mandeeps/SU-WaterCam/tools/transmit_ip.py

"""IP uplink/downlink transport for SU-WaterCam.

Sends sensor channel data to the WaterCam FastAPI server over HTTP (WiFi or
cellular) and polls for queued downlink commands.  Designed to run outside of
TickTalkPython so the logic can be tested standalone before integration.

Usage (module)
--------------
    from tools.transmit_ip import IPTransmitter
    tx = IPTransmitter()                  # reads runtime_config.json
    result = tx.send_uplink(channels)     # {"success": bool, "status_code": int|None, ...}
    reply  = tx.poll_downlink()           # {"success": bool, "status_code": int|None, "command": dict|None, ...}
    cmd    = reply["command"]             # dict or None

Usage (CLI smoke-test)
----------------------
    python tools/transmit_ip.py

Configuration
-------------
All settings live in runtime_config.json under the "ip_upload" key.  See the
project docs/IP_TRANSMISSION.md for a full field reference.

Channel format
--------------
Each element of `channels` must match the ChannelItem schema the server expects:
    {"code": "02 01", "payload_hex": "00000064"}

Codes used by this device (from API CHANNEL_REGISTRY):
    "00 01"  device_ts        (8 bytes, UNIX seconds as u64 big-endian)
    "02 01"  battery_pct      (4 bytes, uint32)
    "03 01"  imu_block        (12 bytes)
    "04 01"  gps_block        (8 bytes: lat int32 /1e6, lon int32 /1e6)
    "05 01"  temperature_c    (2 bytes, int16 /100.0)
    "06 01"  humidity_pct     (1 byte, uint8)
    "07 17"  camera_flood_detect  (4 bytes, bool as uint32)
    "07 27"  camera_new_local_max (4 bytes, bool as uint32)
    "08 18"  camera_flood_bitmap  (variable length, raw bitmap bytes as hex string)
    "09 19"  sr_area_threshold_pct        (4 bytes)
    "09 29"  sr_stage_threshold_cm        (4 bytes)
    "09 39"  sr_monitoring_frequency      (4 bytes)
    "09 49"  sr_emergency_frequency       (4 bytes)
    "09 59"  sr_neighborhood_emerg_freq   (4 bytes)
"""

from __future__ import annotations

import json
import logging
import os
import subprocess
import time
from typing import Any, Callable, Dict, List, Optional

import requests

logger = logging.getLogger(__name__)

# Default config path — relative to the project root (one level above tools/).
_DEFAULT_CONFIG_PATH = os.path.join(
    os.path.dirname(__file__), "..", "runtime_config.json"
)

# Pending-uplink queue directory — persists failed readings for retry next cycle.
_DEFAULT_QUEUE_DIR = os.path.join(
    os.path.dirname(__file__), "..", "data", "ip_uplink_pending"
)


def _coerce_int(value: Any, default: int) -> int:
    """Return ``int(value)`` or ``default`` if value is missing/invalid."""
    try:
        return int(value)
    except (TypeError, ValueError):
        return default


def _coerce_float(value: Any, default: float) -> float:
    """Return ``float(value)`` or ``default`` if value is missing/invalid."""
    try:
        return float(value)
    except (TypeError, ValueError):
        return default


def _load_ip_config(config_path: str = _DEFAULT_CONFIG_PATH) -> Dict[str, Any]:
    """Load and return the ip_upload section from runtime_config.json.

    Returns an empty dict (all defaults) if the file is missing or contains
    invalid JSON — runtime_config.json is gitignored and may not exist in fresh
    dev or CI environments.
    """
    try:
        with open(config_path) as f:
            cfg = json.load(f)
    except OSError as exc:
        # Covers FileNotFoundError, PermissionError, and other I/O failures.
        logger.debug("Cannot read config at %s (%s); using defaults", config_path, exc)
        return {}
    except json.JSONDecodeError as exc:
        logger.warning("Invalid JSON in %s: %s; using defaults", config_path, exc)
        return {}
    if not isinstance(cfg, dict):
        logger.warning("Unexpected config format in %s; using defaults", config_path)
        return {}
    ip_cfg = cfg.get("ip_upload", {})
    if not isinstance(ip_cfg, dict):
        logger.warning("ip_upload in %s is not an object; using defaults", config_path)
        return {}
    return ip_cfg


class IPTransmitter:
    """Handles uplink posting and downlink polling over HTTP.

    Parameters
    ----------
    config_path:
        Path to runtime_config.json.  Defaults to the project-root copy.
    override_url:
        If provided, overrides the server_url from config (useful in tests).
    override_device_id:
        If provided, overrides the device_id from config.

    Notes
    -----
    ``self.enabled`` reflects the ``ip_upload.enabled`` config flag, but
    ``send_uplink()`` and ``poll_downlink()`` do **not** check it internally —
    the flag is an integration-layer concern enforced by ``ticktalk_main.py``.
    Direct callers (tests, CLI smoke-test) are responsible for checking
    ``tx.enabled`` themselves if they want to respect the flag.
    """

    def __init__(
        self,
        config_path: str = _DEFAULT_CONFIG_PATH,
        override_url: Optional[str] = None,
        override_device_id: Optional[str] = None,
        queue_dir: Optional[str] = None,
    ) -> None:
        cfg = _load_ip_config(config_path)

        self.enabled: bool = cfg.get("enabled", False)
        self.server_url: str = (override_url or cfg.get("server_url", "http://localhost:8000")).rstrip("/")
        self.api_key: str = cfg.get("api_key", "")
        self.device_id: str = override_device_id or cfg.get("device_id", "watercam-001")
        self.timeout_s: int = max(1, _coerce_int(cfg.get("timeout_s"), 15))
        self.retry_attempts: int = max(1, _coerce_int(cfg.get("retry_attempts"), 3))
        self.retry_backoff_s: float = _coerce_float(cfg.get("retry_backoff_s"), 2.0)
        self.fallback_to_lora: bool = cfg.get("fallback_to_lora", True)
        self.max_queue_depth: int = max(1, _coerce_int(cfg.get("max_queue_depth"), 48))
        self.max_queue_age_days: float = max(0.0, _coerce_float(cfg.get("max_queue_age_days"), 7.0))
        # Transport order LoRa -> WiFi -> cellular: skip the IP uplink while
        # the mDot is joined, and use the named NetworkManager connection only
        # when the server can't be reached without it.
        self.only_if_lora_unavailable: bool = cfg.get("only_if_lora_unavailable", True) is not False
        cell = cfg.get("cellular_connection", "Quectel")
        self.cellular_connection: str = cell if isinstance(cell, str) else ""
        self.cellular_connect_timeout_s: int = max(5, _coerce_int(cfg.get("cellular_connect_timeout_s"), 90))
        self._queue_dir: str = os.path.abspath(queue_dir or _DEFAULT_QUEUE_DIR)

        self._session = requests.Session()
        if self.api_key:
            self._session.headers.update({"Authorization": f"Bearer {self.api_key}"})
        self._session.headers.update({"Content-Type": "application/json"})

    # ------------------------------------------------------------------ #
    # Public API                                                           #
    # ------------------------------------------------------------------ #

    def send_uplink(
        self,
        channels: List[Dict[str, str]],
        device_ts: Optional[int] = None,
    ) -> Dict[str, Any]:
        """POST sensor channel data to /ip/uplink.

        Parameters
        ----------
        channels:
            List of channel dicts, each with "code" and "payload_hex".
            Example:
                [
                    {"code": "02 01", "payload_hex": "00000064"},
                    {"code": "05 01", "payload_hex": "0B80"},
                ]
        device_ts:
            Optional UNIX epoch (seconds) timestamp from the device clock.
            When provided, the server uses it as the measurement timestamp
            instead of the server arrival time.

        Returns
        -------
        dict with keys:
            "success"    : bool
            "status_code": int or None
            "response"   : decoded JSON body or None
            "error"      : error message string or None
            "attempts"   : number of attempts made
        """
        if not channels:
            return _err_result("send_uplink called with empty channels list")

        payload: Dict[str, Any] = {
            "device_id": self.device_id,
            "channels": channels,
        }
        if device_ts is not None:
            payload["device_ts"] = device_ts

        url = f"{self.server_url}/ip/uplink"
        return self._post_with_retry(url, payload)

    def poll_downlink(self) -> Dict[str, Any]:
        """GET /ip/downlink/{device_id} to retrieve the oldest pending command.

        The server atomically marks the command as delivered on retrieval, so
        calling this multiple times without handling the first response will
        consume queued commands.

        Returns
        -------
        dict with keys:
            "success"    : bool
            "command"    : dict or None  (None means no pending command)
            "status_code": int or None
            "error"      : error message string or None
        """
        url = f"{self.server_url}/ip/downlink/{self.device_id}"

        try:
            resp = self._session.get(url, timeout=self.timeout_s)
        except requests.exceptions.ConnectionError as exc:
            return {"success": False, "command": None, "status_code": None,
                    "error": f"Connection error: {exc}"}
        except requests.exceptions.Timeout:
            return {"success": False, "command": None, "status_code": None,
                    "error": f"Request timed out after {self.timeout_s}s"}
        except requests.exceptions.RequestException as exc:
            return {"success": False, "command": None, "status_code": None,
                    "error": str(exc)}

        if resp.status_code == 404:
            # Device not yet registered on the server — treat as "no pending commands"
            # rather than a transport error, so callers handle it uniformly.
            return {
                "success": True,
                "command": None,
                "status_code": resp.status_code,
                "error": None,
            }

        if resp.status_code != 200:
            return {
                "success": False,
                "command": None,
                "status_code": resp.status_code,
                "error": f"HTTP {resp.status_code}: {resp.text[:200]}",
            }

        try:
            body = resp.json()
        except ValueError:
            return {"success": False, "command": None,
                    "status_code": resp.status_code,
                    "error": "Non-JSON response from server"}

        return {
            "success": True,
            "command": body.get("command"),   # dict or None
            "status_code": resp.status_code,
            "error": None,
        }

    def is_reachable(self, timeout_s: Optional[float] = None) -> bool:
        """Quick check — returns True if the server /health endpoint responds.

        Parameters
        ----------
        timeout_s:
            Override the instance timeout for this call only.  Pass a small
            value (e.g. 3) in CI/test contexts to fail fast when the server
            is not running.
        """
        t = timeout_s if timeout_s is not None else self.timeout_s
        try:
            resp = self._session.get(f"{self.server_url}/health", timeout=t)
            return resp.status_code == 200
        except requests.exceptions.RequestException:
            return False

    def wait_reachable(self, deadline_s: float, probe_timeout_s: float = 5) -> bool:
        """Probe /health until it answers or ``deadline_s`` seconds have passed."""
        end = time.monotonic() + deadline_s
        while True:
            if self.is_reachable(timeout_s=probe_timeout_s):
                return True
            if time.monotonic() >= end:
                return False
            time.sleep(2)

    def close(self) -> None:
        """Close the underlying requests.Session and release pooled connections."""
        self._session.close()

    # ------------------------------------------------------------------ #
    # Store-and-forward queue                                              #
    # ------------------------------------------------------------------ #

    def _enqueue(self, channels: List[Dict[str, str]], device_ts: int) -> bool:
        """Persist a failed uplink to the pending queue for retry next cycle.

        Writes an atomic JSON file to ``self._queue_dir``.  If the queue is
        already at ``max_queue_depth``, the oldest entry is dropped to make
        room.  Returns True on success, False on I/O error.
        """
        try:
            os.makedirs(self._queue_dir, exist_ok=True)
            existing = sorted(
                f for f in os.listdir(self._queue_dir) if f.endswith(".json")
            )
            while len(existing) >= self.max_queue_depth:
                try:
                    os.unlink(os.path.join(self._queue_dir, existing.pop(0)))
                except OSError:
                    pass
            record = {
                "channels": channels,
                "device_ts": device_ts,
                "enqueued_at": time.time(),
            }
            fname = f"{device_ts}_{len(existing):06d}.json"
            tmp_path = os.path.join(self._queue_dir, fname + ".tmp")
            final_path = os.path.join(self._queue_dir, fname)
            with open(tmp_path, "w") as f:
                json.dump(record, f)
            os.replace(tmp_path, final_path)
            logger.info("Queued uplink to %s (%d channels)", fname, len(channels))
            return True
        except OSError as exc:
            logger.warning("Failed to enqueue uplink: %s", exc)
            return False

    def _drain_queue(self) -> Dict[str, Any]:
        """Send queued entries oldest-first; stop on first send failure.

        Returns a dict with keys:
            "drained"    : int            — number of entries successfully sent
            "failed"     : bool           — True if a send failed mid-drain
            "failed_file": Optional[str]  — filename of the entry that failed
            "drained_ts" : List[int]      — device_ts of each entry sent
        """
        result: Dict[str, Any] = {"drained": 0, "failed": False, "failed_file": None, "drained_ts": []}
        try:
            entries = sorted(
                f for f in os.listdir(self._queue_dir) if f.endswith(".json")
            )
        except FileNotFoundError:
            return result

        cutoff = time.time() - self.max_queue_age_days * 86400

        for fname in entries:
            path = os.path.join(self._queue_dir, fname)
            try:
                with open(path) as f:
                    record = json.load(f)
            except (OSError, ValueError):
                logger.warning("Dropping corrupt queue file: %s", fname)
                try:
                    os.unlink(path)
                except OSError:
                    pass
                continue

            if record.get("enqueued_at", 0) < cutoff:
                logger.info("Evicting stale queue entry: %s", fname)
                try:
                    os.unlink(path)
                except OSError:
                    pass
                continue

            send_result = self.send_uplink(
                record["channels"], device_ts=record.get("device_ts")
            )
            if send_result["success"]:
                try:
                    os.unlink(path)
                except OSError:
                    pass
                result["drained"] += 1
                if record.get("device_ts") is not None:
                    result["drained_ts"].append(record["device_ts"])
            else:
                logger.warning("Drain failed on %s: %s", fname, send_result.get("error"))
                result["failed"] = True
                result["failed_file"] = fname
                break

        return result

    # ------------------------------------------------------------------ #
    # Internal helpers                                                     #
    # ------------------------------------------------------------------ #

    def _post_with_retry(
        self, url: str, payload: Dict[str, Any]
    ) -> Dict[str, Any]:
        """POST payload to url with exponential backoff retry.

        Sleep before retry N is ``retry_backoff_s * 2^(N-1)`` seconds, so for
        the default ``retry_backoff_s=2`` and ``retry_attempts=3``:
        attempt 1 → immediate, attempt 2 → 2 s, attempt 3 → 4 s.
        """
        last_error: str = "unknown error"
        last_status: Optional[int] = None

        for attempt in range(1, self.retry_attempts + 1):
            try:
                resp = self._session.post(
                    url, json=payload, timeout=self.timeout_s
                )
                last_status = resp.status_code

                if resp.status_code in (200, 201):
                    try:
                        body = resp.json()
                    except ValueError:
                        body = {"raw": resp.text}
                    logger.info(
                        "IP uplink OK (attempt %d/%d): %s",
                        attempt, self.retry_attempts, resp.status_code,
                    )
                    return {
                        "success": True,
                        "status_code": resp.status_code,
                        "response": body,
                        "error": None,
                        "attempts": attempt,
                    }

                # Server-side error — don't retry 4xx (client mistake)
                if 400 <= resp.status_code < 500:
                    logger.error(
                        "IP uplink rejected by server (HTTP %d): %s",
                        resp.status_code, resp.text[:300],
                    )
                    return _err_result(
                        f"HTTP {resp.status_code}: {resp.text[:200]}",
                        status_code=resp.status_code,
                        attempts=attempt,
                    )

                # 5xx — retry
                last_error = f"HTTP {resp.status_code}: {resp.text[:200]}"
                logger.warning(
                    "IP uplink attempt %d/%d failed with %d, retrying...",
                    attempt, self.retry_attempts, resp.status_code,
                )

            except requests.exceptions.ConnectionError as exc:
                last_error = f"Connection error: {exc}"
                logger.warning(
                    "IP uplink attempt %d/%d connection error: %s",
                    attempt, self.retry_attempts, exc,
                )
            except requests.exceptions.Timeout:
                last_error = f"Timeout after {self.timeout_s}s"
                logger.warning(
                    "IP uplink attempt %d/%d timed out", attempt, self.retry_attempts
                )
            except requests.exceptions.RequestException as exc:
                last_error = str(exc)
                logger.warning(
                    "IP uplink attempt %d/%d request error: %s",
                    attempt, self.retry_attempts, exc,
                )

            if attempt < self.retry_attempts:
                sleep_s = self.retry_backoff_s * (2 ** (attempt - 1))
                logger.debug("Waiting %.1fs before retry %d", sleep_s, attempt + 1)
                time.sleep(sleep_s)

        logger.error(
            "IP uplink failed after %d attempts. Last error: %s",
            self.retry_attempts, last_error,
        )
        return _err_result(
            last_error,
            status_code=last_status,
            attempts=self.retry_attempts,
        )


# ------------------------------------------------------------------ #
# Module-level convenience functions                                   #
# ------------------------------------------------------------------ #

def send_uplink(
    channels: List[Dict[str, str]],
    device_ts: Optional[int] = None,
    config_path: str = _DEFAULT_CONFIG_PATH,
) -> Dict[str, Any]:
    """Module-level wrapper: create a transmitter, send one uplink, then close."""
    tx = IPTransmitter(config_path=config_path)
    try:
        return tx.send_uplink(channels, device_ts=device_ts)
    finally:
        tx.close()


def poll_downlink(config_path: str = _DEFAULT_CONFIG_PATH) -> Dict[str, Any]:
    """Module-level wrapper: create a transmitter, poll for one downlink, then close."""
    tx = IPTransmitter(config_path=config_path)
    try:
        return tx.poll_downlink()
    finally:
        tx.close()


# Downlink command codes and their payload lengths, as the server encodes them
# (app/encoders.py): a frame is one or more [code: 2 bytes][value: fixed width],
# with no length byte. The same frames arrive over IP (as parts) and over LoRa
# (as raw bytes, see parse_downlink_frame), so this is the one table for both.
DOWNLINK_CODE_LENGTHS: Dict[str, int] = {
    "10 90": 1,    # area_threshold_pct
    "11 91": 2,    # stage_threshold_cm (u16)
    "12 92": 1,    # monitoring_freq_h index
    "13 93": 1,    # emergency_freq_min index
    "14 94": 1,    # flood_code_freq_min index
    "16 96": 1,    # audio_recording_enabled
    "18 98": 1,    # remote debug session: NN x 10 min, 0 = end (docs/REMOTE_DEBUG_SESSION.md)
    "21 91": 1,    # emergency on for HH hours (00 = emergency_max_hours)
    "21": 0,       # emergency on, from before 21 91; kept while nodes and API update (IP only)
    "99 99": 0,    # emergency off: the same 0x99 0x99 as over LoRa
}


def parse_downlink_frame(data: bytes) -> List[Dict[str, str]] | None:
    """Split a raw server frame into parts for apply_downlink_command().

    Returns None unless the whole frame is a sequence of known two-byte codes,
    each followed by exactly its value width, so other payload formats are left
    to their own parsers.
    """
    parts: List[Dict[str, str]] = []
    i = 0
    while i < len(data):
        if i + 2 > len(data):
            return None
        code = f"{data[i]:02x} {data[i + 1]:02x}"
        width = DOWNLINK_CODE_LENGTHS.get(code)
        if width is None:
            return None
        value = data[i + 2:i + 2 + width]
        if len(value) != width:
            return None
        parts.append({"code": code, "payload_hex": value.hex()})
        i += 2 + width
    return parts or None


def apply_downlink_command(
    cmd: Dict[str, Any],
    set_param_fn: Callable[[str, Any], None] | None = None,
) -> Dict[str, Any]:
    """Decode a downlink command dict and apply each recognised parameter change.

    This is the standalone-tools counterpart to the TickTalkPython
    ``ip_downlink_poll_and_apply`` action in ``ticktalk_main.py``.  It contains
    no TickTalkPython dependencies and can be called from tests, CLI scripts, or
    any future integration layer.

    Parameters
    ----------
    cmd:
        The dict at ``poll_downlink()["command"]``.  Must have a ``"parts"``
        field — a list of ``{"code": str, "payload_hex": str}`` dicts.
    set_param_fn:
        ``Callable[[str, Any], None]`` used to persist each change.  Defaults
        to ``tools.lora_runtime_integration.set_parameter``.  Pass a custom
        function in tests to avoid touching the real runtime config.

    Returns
    -------
    dict with keys:
        "applied" : list[str] — "param=value" strings for each change applied
        "skipped" : list[str] — string identifiers for skipped parts: the
            command code when available, otherwise a stringified malformed part
            or invalid code value
        "queue_id": the queue_id from cmd, or None
    """
    if set_param_fn is None:
        try:
            from tools.lora_runtime_integration import set_parameter as set_param_fn
        except ImportError as exc:
            raise RuntimeError(
                "apply_downlink_command: set_param_fn not provided and "
                "tools.lora_runtime_integration is unavailable. "
                "Pass set_param_fn explicitly when calling outside TickTalkPython."
            ) from exc

    # Index-based lookup tables — must match server app/encoders.py constants.
    _MF_HOURS = [1, 3, 6, 24, 72]       # monitoring_freq_h allowed values
    _EF_MIN   = [2, 5, 10]              # emergency_freq_min allowed values
    _FF_MIN   = [10, 20, 30, 40, 50, 60]  # flood_code_freq_min allowed values

    _expected_len = DOWNLINK_CODE_LENGTHS

    parts_raw = cmd.get("parts")
    if parts_raw is None:
        parts: list = []
    elif isinstance(parts_raw, list):
        parts = parts_raw
    else:
        logger.warning(
            "apply_downlink_command: malformed parts field "
            "(expected list, got %s) — treating as empty",
            type(parts_raw).__name__,
        )
        parts = []

    applied: List[str] = []
    skipped: List[str] = []

    for part in parts:
        if not isinstance(part, dict):
            logger.warning(
                "apply_downlink_command: malformed part (expected dict, got %s) — skipping",
                type(part).__name__,
            )
            skipped.append("<malformed_part>")
            continue

        code_raw = part.get("code", "")
        payload_hex = part.get("payload_hex", "")
        if not isinstance(code_raw, str) or not isinstance(payload_hex, str):
            logger.warning(
                "apply_downlink_command: non-string code or payload_hex in part %s — skipping",
                part,
            )
            skipped.append(str(code_raw))
            continue
        code = code_raw.strip()
        if not code:
            logger.warning(
                "apply_downlink_command: missing or empty code in part %s — skipping", part
            )
            skipped.append("<missing_code>")
            continue

        try:
            payload_bytes = bytes.fromhex(payload_hex)
        except (TypeError, ValueError):
            logger.warning(
                "apply_downlink_command: bad payload_hex in part %s — skipping", part
            )
            skipped.append(code)
            continue

        if code in _expected_len and len(payload_bytes) != _expected_len[code]:
            logger.warning(
                "apply_downlink_command: wrong payload length for %s "
                "(expected %d, got %d) — skipping",
                code, _expected_len[code], len(payload_bytes),
            )
            skipped.append(code)
            continue

        if code == "10 90":  # area_threshold_pct — direct u8 value
            val = int.from_bytes(payload_bytes, "big")
            set_param_fn("area_threshold", val)
            logger.info("Applied: area_threshold = %d%%", val)
            applied.append(f"area_threshold={val}%")

        elif code == "11 91":  # stage_threshold_cm — u16 big-endian
            val_cm = int.from_bytes(payload_bytes, "big")
            set_param_fn("stage_threshold", val_cm)
            logger.info("Applied: stage_threshold = %dcm", val_cm)
            applied.append(f"stage_threshold={val_cm}cm")

        elif code == "12 92":  # monitoring_freq_h — u8 index into _MF_HOURS
            idx = int.from_bytes(payload_bytes, "big")
            if 0 <= idx < len(_MF_HOURS):
                hours = _MF_HOURS[idx]
                set_param_fn("monitoring_frequency", hours * 60)  # stored in minutes
                logger.info("Applied: monitoring_frequency = %dh (%dmin)", hours, hours * 60)
                applied.append(f"monitoring_frequency={hours}h")
            else:
                logger.warning("apply_downlink_command: monitoring_freq index %d out of range", idx)
                skipped.append(code)

        elif code == "13 93":  # emergency_freq_min — u8 index into _EF_MIN
            idx = int.from_bytes(payload_bytes, "big")
            if 0 <= idx < len(_EF_MIN):
                mins = _EF_MIN[idx]
                set_param_fn("emergency_frequency", mins)
                logger.info("Applied: emergency_frequency = %dmin", mins)
                applied.append(f"emergency_frequency={mins}min")
            else:
                logger.warning("apply_downlink_command: emergency_freq index %d out of range", idx)
                skipped.append(code)

        elif code == "14 94":  # flood_code_freq_min — u8 index into _FF_MIN
            idx = int.from_bytes(payload_bytes, "big")
            if 0 <= idx < len(_FF_MIN):
                mins = _FF_MIN[idx]
                set_param_fn("neighborhood_emergency_frequency", mins)
                logger.info("Applied: neighborhood_emergency_frequency = %dmin", mins)
                applied.append(f"neighborhood_emergency_frequency={mins}min")
            else:
                logger.warning("apply_downlink_command: flood_code_freq index %d out of range", idx)
                skipped.append(code)

        elif code == "16 96":  # audio_recording_enabled — direct u8 bool (0/1)
            val = bool(int.from_bytes(payload_bytes, "big"))
            set_param_fn("audio_recording_enabled", val)
            logger.info("Applied: audio_recording_enabled = %s", val)
            applied.append(f"audio_recording_enabled={val}")

        elif code == "18 98":  # remote debug session (Tailscale over cellular)
            # Run by remote-debug.timer, not here: starting a session stops
            # ticktalk, which is the process running this.
            try:
                from tools import remote_debug
            except ImportError:
                import remote_debug
            minutes = remote_debug.minutes_from_code(f"{payload_bytes[0]:02x}")
            remote_debug.request(minutes, "ip")
            logger.info("Queued: remote debug %s", f"{minutes} min" if minutes else "end")
            applied.append(f"remote_debug={minutes}")

        elif code == "21 91":  # emergency mode on for HH hours
            hours = payload_bytes[0]
            if hours:
                set_param_fn("emergency_max_hours", min(hours, 168))
            set_param_fn("emergency_mode", True)
            set_param_fn("emergency_since", time.time())   # the duration starts now
            logger.info("Applied: emergency_mode = True for %s h", hours or "default")
            applied.append(f"emergency_mode=True({hours or 'default'}h)")

        elif code == "21":  # emergency mode on: the API's code before 21 91
            set_param_fn("emergency_mode", True)
            logger.info("Applied: emergency_mode = True")
            applied.append("emergency_mode=True")

        elif code == "99 99":  # emergency mode off
            set_param_fn("emergency_mode", False)
            logger.info("Applied: emergency_mode = False")
            applied.append("emergency_mode=False")

        else:
            logger.warning("apply_downlink_command: unrecognised code '%s' — ignoring", code)
            skipped.append(code)

    return {
        "applied": applied,
        "skipped": skipped,
        "queue_id": cmd.get("queue_id"),
    }


# ------------------------------------------------------------------ #
# Internal util                                                        #
# ------------------------------------------------------------------ #

def cellular_status(connection: str) -> Dict[str, bool]:
    """Whether the NetworkManager connection exists, is active, and autoconnects.

    Only a connection with autoconnect off is managed on demand; one that
    autoconnects is meant to stay up and is left alone.
    """
    status = {"exists": False, "active": False, "autoconnect": False}
    try:
        r = subprocess.run(
            ["nmcli", "-g", "connection.autoconnect,GENERAL.STATE", "connection", "show", connection],
            capture_output=True, text=True, timeout=15,
        )
    except (OSError, subprocess.TimeoutExpired) as exc:
        logger.warning("nmcli connection show %s failed: %s", connection, exc)
        return status
    if r.returncode != 0:
        return status
    lines = r.stdout.splitlines()
    status["exists"] = True
    status["autoconnect"] = bool(lines) and lines[0].strip() == "yes"
    status["active"] = len(lines) > 1 and lines[1].strip() == "activated"
    return status


def wifi_connected() -> bool:
    """True if a WiFi device is connected (NetworkManager prefers its route)."""
    try:
        r = subprocess.run(["nmcli", "-t", "-f", "TYPE,STATE", "device"],
                           capture_output=True, text=True, timeout=15)
    except (OSError, subprocess.TimeoutExpired):
        return False
    return any(line == "wifi:connected" for line in r.stdout.splitlines())


def cellular_up(connection: str, timeout_s: int = 90) -> bool:
    """Activate a NetworkManager connection (the LTE modem's); True once it is up.

    The connection should have autoconnect off, so the modem stays registered
    but carries no data until a wake has no other route to the server.
    """
    try:
        r = subprocess.run(
            ["nmcli", "--wait", str(timeout_s), "connection", "up", connection],
            capture_output=True, text=True, timeout=timeout_s + 10,
        )
    except (OSError, subprocess.TimeoutExpired) as exc:
        logger.warning("nmcli connection up %s failed: %s", connection, exc)
        return False
    if r.returncode != 0:
        logger.warning("nmcli connection up %s: %s", connection, (r.stderr or r.stdout).strip())
    return r.returncode == 0


def cellular_down(connection: str) -> None:
    """Deactivate the connection again; never raises."""
    try:
        subprocess.run(["nmcli", "connection", "down", connection],
                       capture_output=True, text=True, timeout=30)
    except (OSError, subprocess.TimeoutExpired) as exc:
        logger.warning("nmcli connection down %s failed: %s", connection, exc)


def _err_result(
    message: str,
    status_code: Optional[int] = None,
    attempts: int = 0,
) -> Dict[str, Any]:
    return {
        "success": False,
        "status_code": status_code,
        "response": None,
        "error": message,
        "attempts": attempts,
    }


# ------------------------------------------------------------------ #
# CLI smoke-test                                                       #
# ------------------------------------------------------------------ #

if __name__ == "__main__":
    logging.basicConfig(level=logging.INFO, format="%(levelname)s: %(message)s")

    import struct

    tx = IPTransmitter()
    print(f"Server : {tx.server_url}")
    print(f"Device : {tx.device_id}")
    print(f"Enabled: {tx.enabled}")
    print()

    # Encode a minimal uplink: battery 75%, temperature 22.50 °C
    battery_hex = struct.pack(">I", 75).hex()            # "0000004B"
    temp_raw = int(22.50 * 100)                          # 2250 → 0x08CA
    temp_hex = struct.pack(">h", temp_raw).hex()         # signed int16
    ts_now = int(time.time())
    ts_hex = struct.pack(">Q", ts_now).hex()             # 8-byte big-endian u64

    channels = [
        {"code": "00 01", "payload_hex": ts_hex},
        {"code": "02 01", "payload_hex": battery_hex},
        {"code": "05 01", "payload_hex": temp_hex},
    ]

    print("--- Uplink test ---")
    print(f"Channels: {json.dumps(channels, indent=2)}")
    result = tx.send_uplink(channels, device_ts=ts_now)
    print(f"Result  : {json.dumps(result, indent=2)}")

    print()
    print("--- Downlink poll ---")
    dl = tx.poll_downlink()
    print(f"Result  : {json.dumps(dl, indent=2)}")
